Baasonen/Vene2.0/CAD/VENE.SLDASM

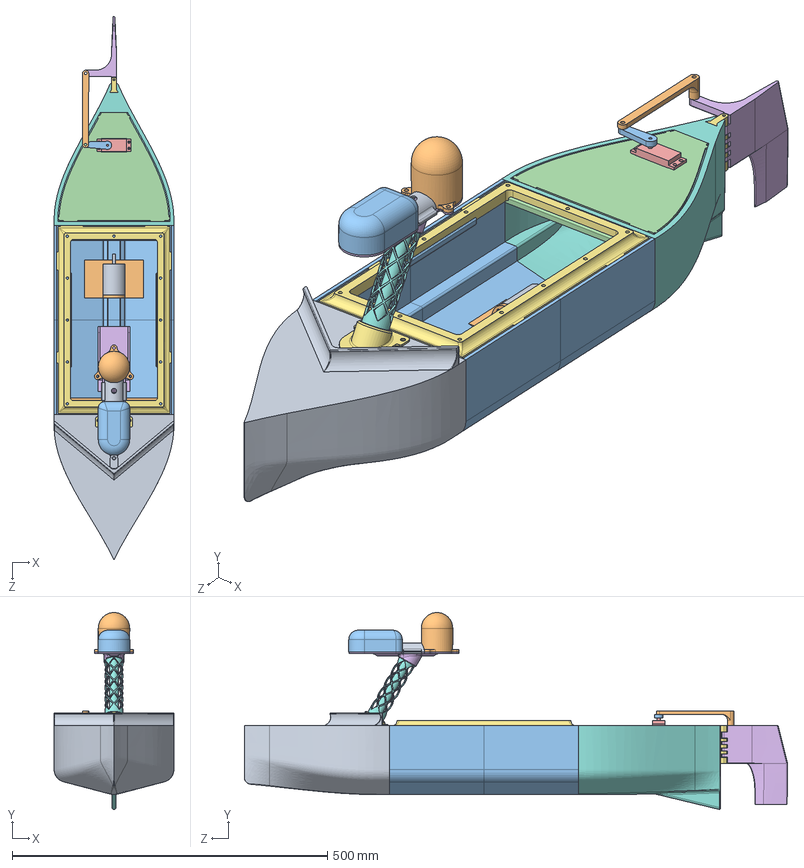
[picture p1: CAD file, 2026-08-04]
CAD/VENE.SLDASM
190.1 x 312.4 x 861.5 mm
HULLMID x 2
MOTORBASE1
MOTORPLACEHOLDER
HULLAFT_2
RUDDERATTACHMENT
RUDDER
SERVO_MG996R
AFT_DECK
SERVO_HORN
RUDDER_LINKAGE
HULLBOW
MAST
MAST_DECK_ATTACHMENT
MAST_END
NEO_6M_BRACKET
NEO_6M_ANTENNA_BRACKET
GPS_SHROUD
LORA_DOME
MAST_END_COVER
PROP_SHAFT_SUPPORT
MAIN_HATCH
BATTER_HOLDER
ESP_HOLDER
HATCH_BRIM_REAR
HATCH_BRIM_SIDE x 2
HATCH_BRIM_FRONT
BOW_PLOW
