Baasonen/Vene2.0/CAD/HULLBOW.SLDPRT

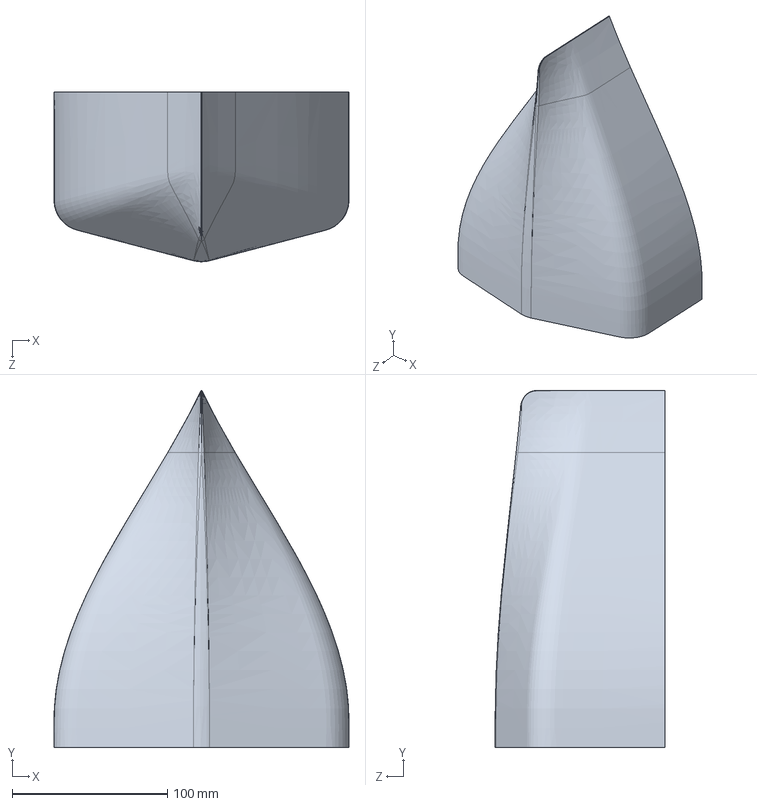
[picture p16: CAD file, 2026-07-09]
CAD/HULLBOW.SLDPRT
190.1 x 230.0 x 109.3 mm
