Baasonen/Vene2.0/CAD/MAST_DECK_ATTACHMENT.SLDPRT

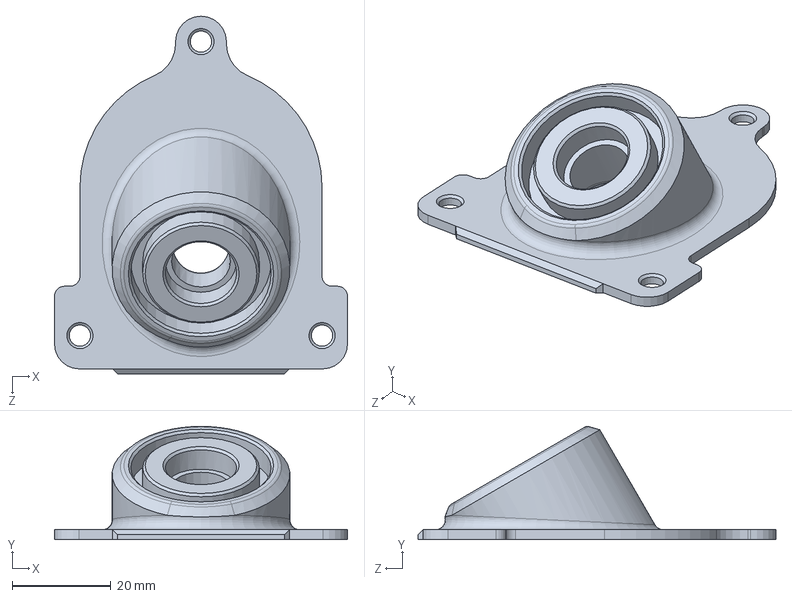
[picture p17: CAD file, 2026-06-03]
CAD/MAST_DECK_ATTACHMENT.SLDPRT
59.3 x 22.9 x 72.4 mm
