Baasonen/Vene2.0/CAD/HULLAFT_2.SLDPRT

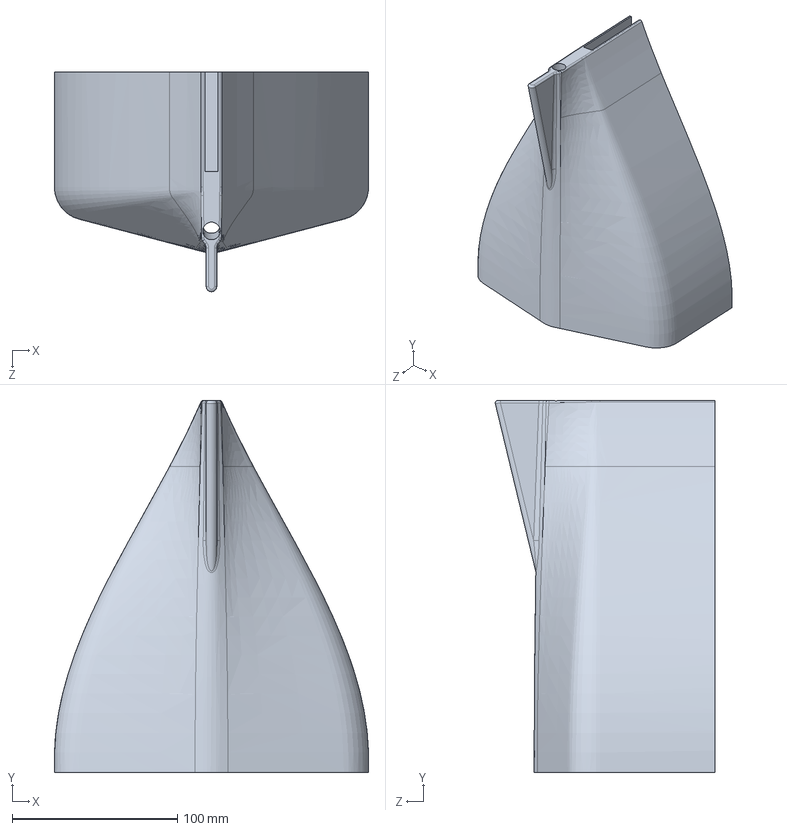
[picture p18: CAD file, 2026-06-03]
CAD/HULLAFT_2.SLDPRT
190.0 x 225.0 x 132.8 mm
