Baasonen/Vene2.0/CAD/PROP_SHAFT_SUPPORT.SLDPRT

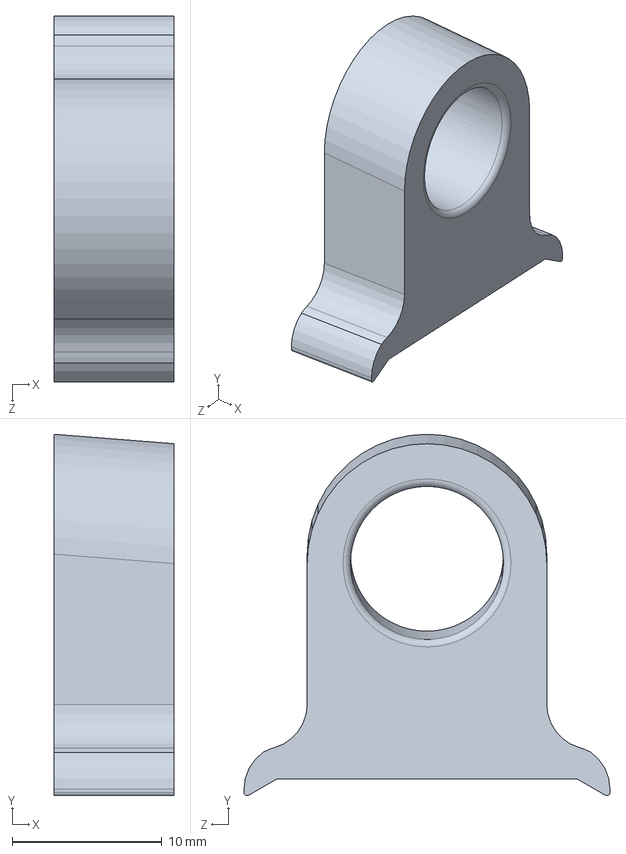
[picture p19: CAD file, 2026-06-03]
CAD/PROP_SHAFT_SUPPORT.SLDPRT
8.00 x 24.1 x 24.4 mm
