Baasonen/Vene2.0/CAD/NEO_6M_ANTENNA_BRACKET.SLDPRT

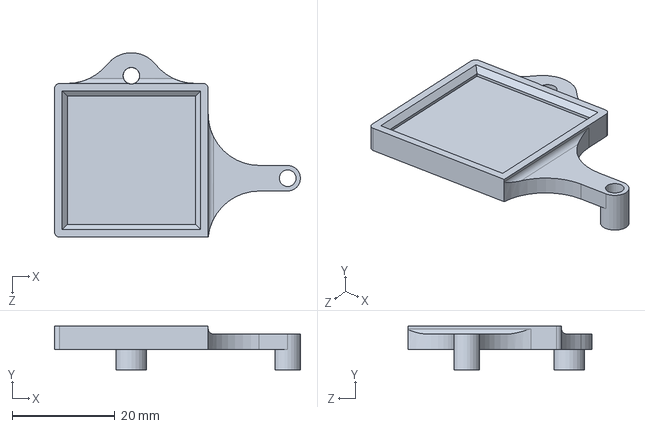
[picture p20: CAD file, 2026-06-03]
CAD/NEO_6M_ANTENNA_BRACKET.SLDPRT
48.0 x 8.50 x 36.0 mm
