Baasonen/Vene2.0/CAD/NEO_6M_BRACKET.SLDPRT

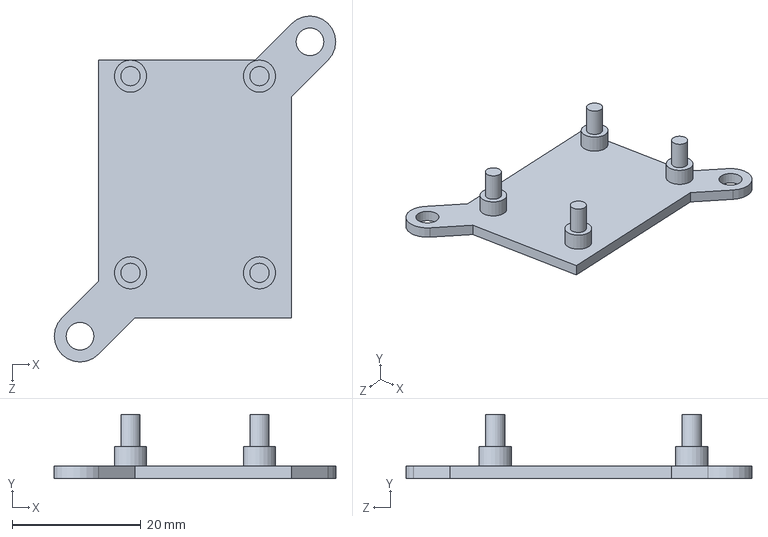
[picture p21: CAD file, 2026-06-03]
CAD/NEO_6M_BRACKET.SLDPRT
43.7 x 10.0 x 53.7 mm
