Baasonen/Vene2.0/CAD/MAST_END.SLDPRT

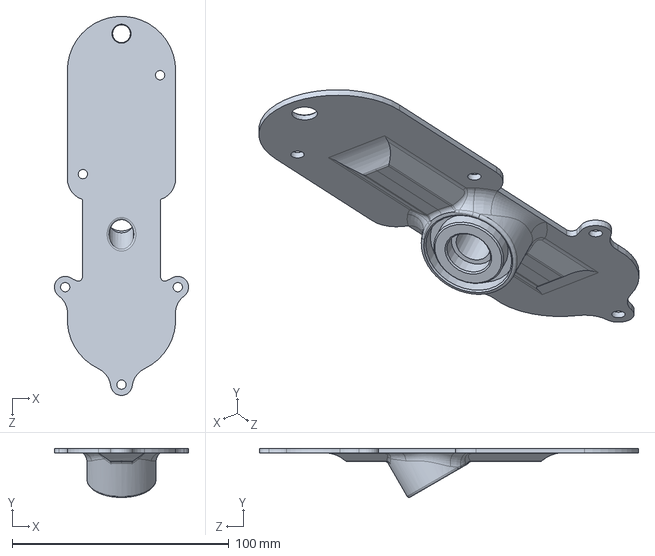
[picture p22: CAD file, 2026-06-03]
CAD/MAST_END.SLDPRT
61.9 x 22.6 x 174.9 mm
