Baasonen/Vene2.0/CAD/MAST_END_COVER.SLDPRT

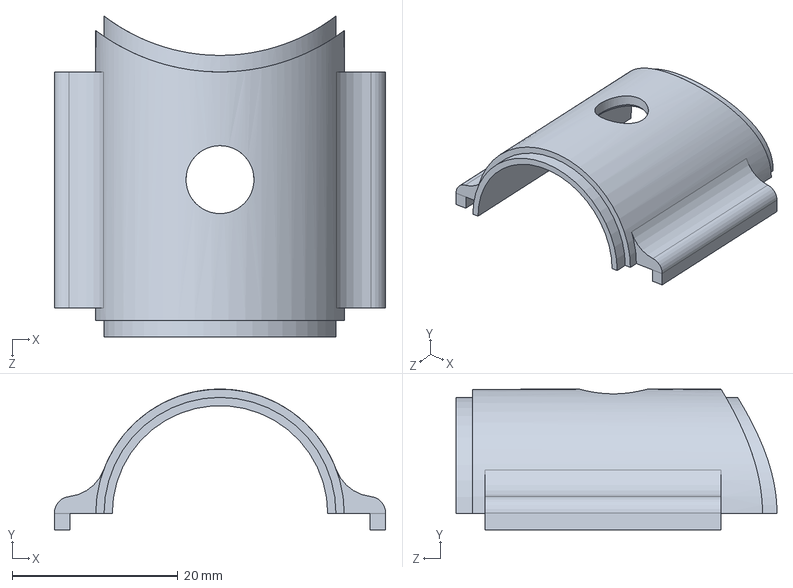
[picture p23: CAD file, 2026-06-03]
CAD/MAST_END_COVER.SLDPRT
40.0 x 17.0 x 38.8 mm
