Baasonen/Vene2.0/CAD/MOTORBASE1.SLDPRT

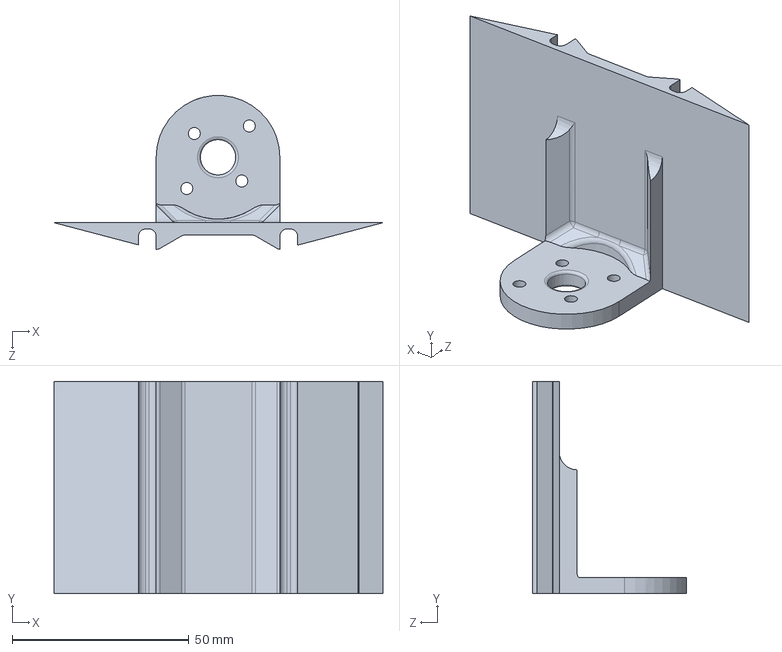
[picture p24: CAD file, 2026-05-25]
CAD/MOTORBASE1.SLDPRT
93.1 x 60.0 x 43.5 mm
