Baasonen/Vene2.0/CAD/RUDDER.SLDPRT

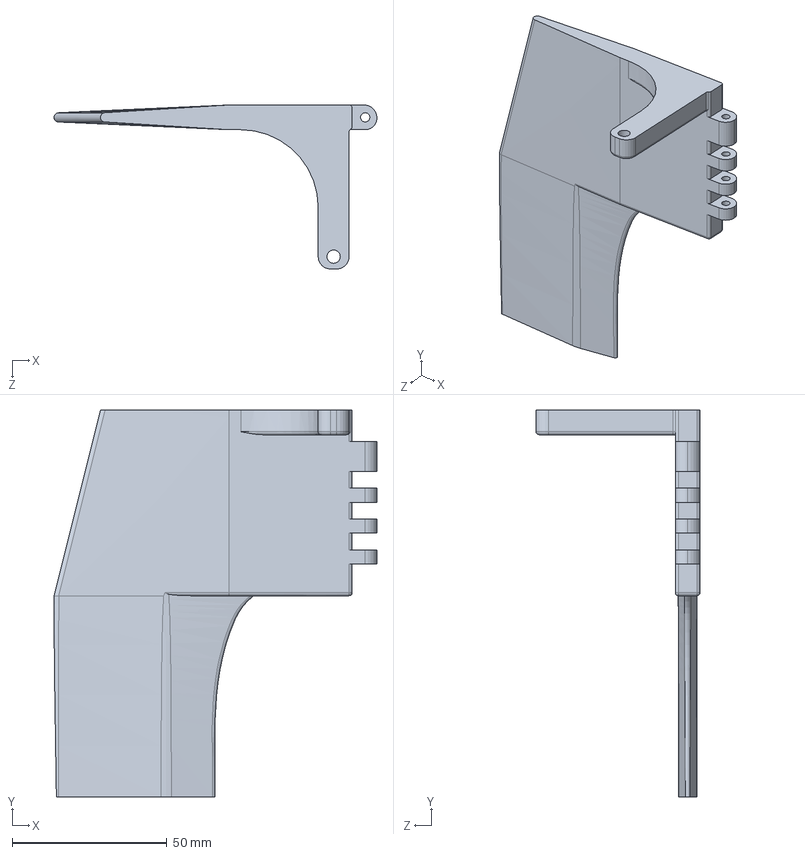
[picture p25: CAD file, 2026-05-25]
CAD/RUDDER.SLDPRT
104.3 x 125.0 x 53.0 mm
