Baasonen/Vene2.0/CAD/RUDDERATTACHMENT.SLDPRT

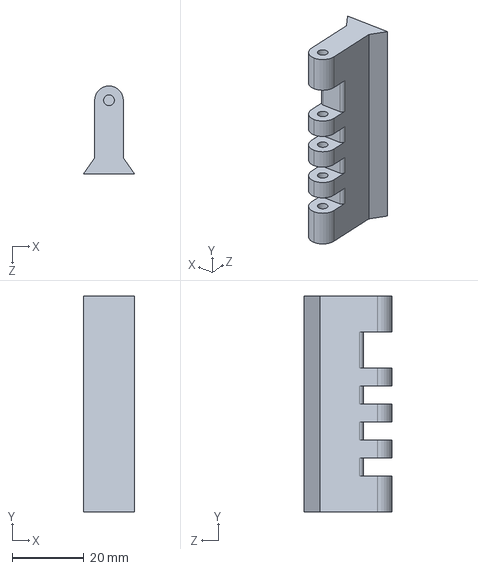
[picture p26: CAD file, 2026-05-25]
CAD/RUDDERATTACHMENT.SLDPRT
14.3 x 60.0 x 24.5 mm
