Baasonen/Vene2.0/CAD/AFT_DECK_GUIDE.SLDPRT

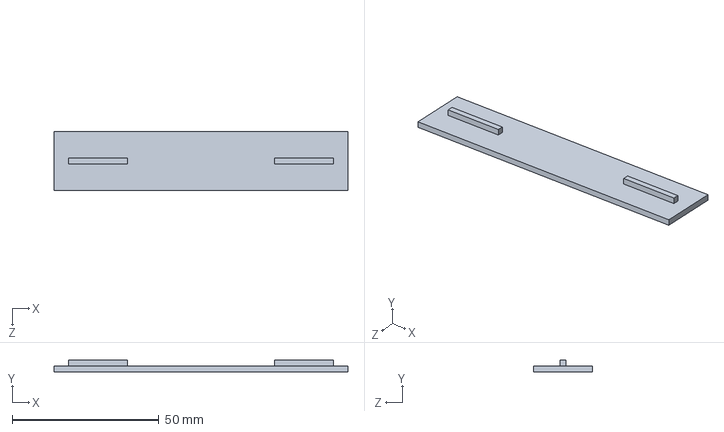
[picture p27: CAD file, 2026-05-25]
CAD/AFT_DECK_GUIDE.SLDPRT
100.0 x 4.00 x 20.0 mm
