Baasonen/Vene2.0/CAD/MAST.SLDPRT

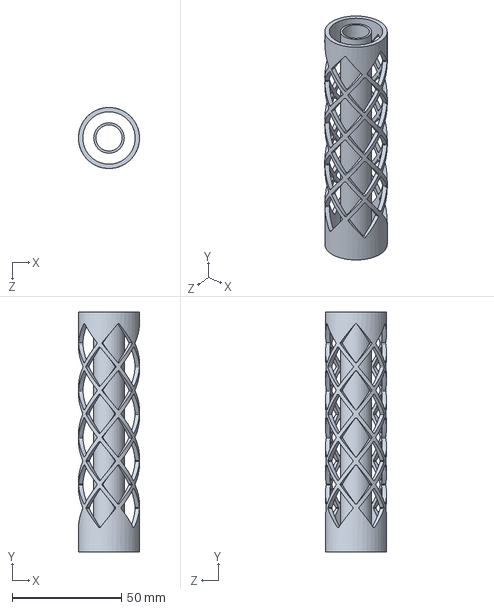
[picture p28: CAD file, 2026-05-25]
CAD/MAST.SLDPRT
28.0 x 110.0 x 28.0 mm
