Baasonen/Vene2.0/CAD/SERVO_HORN.SLDPRT

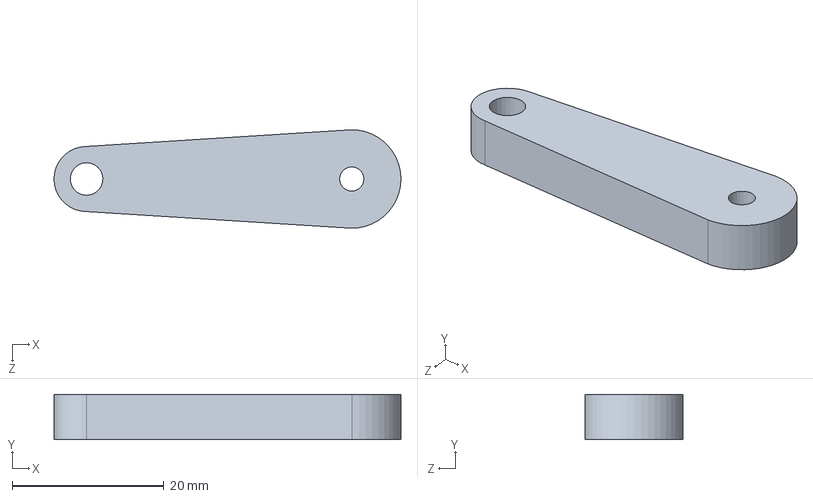
[picture p29: CAD file, 2026-05-25]
CAD/SERVO_HORN.SLDPRT
45.8 x 6.00 x 13.0 mm
