Baasonen/Vene2.0/CAD/HULLMID.SLDPRT

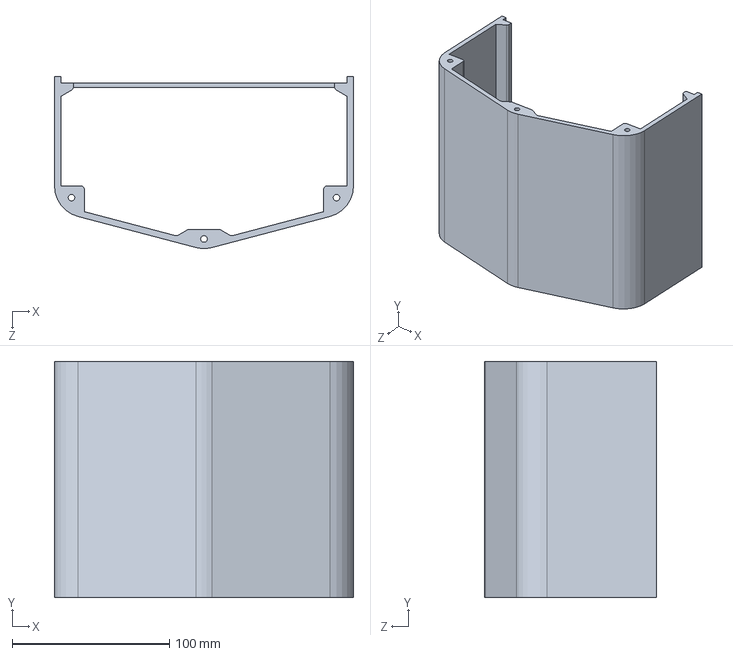
[picture p30: CAD file, 2026-05-25]
CAD/HULLMID.SLDPRT
190.0 x 150.0 x 109.2 mm
