Baasonen/Vene2.0/CAD/SERVO_MG996R.SLDPRT

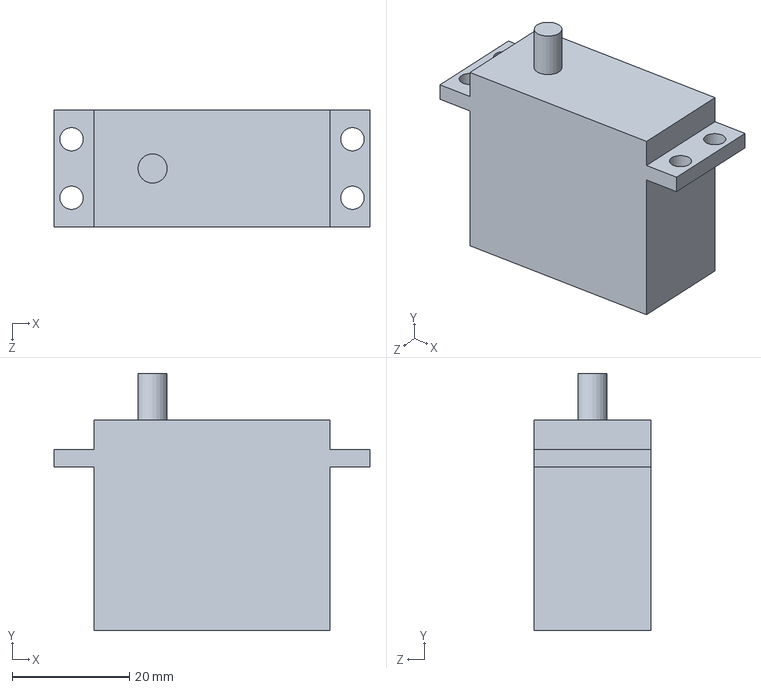
[picture p31: CAD file, 2026-05-25]
CAD/SERVO_MG996R.SLDPRT
54.0 x 44.0 x 20.0 mm
