Baasonen/Vene2.0/CAD/RUDDER_LINKAGE.SLDPRT

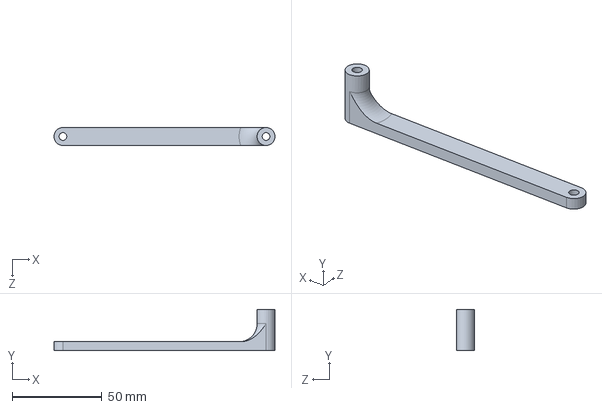
[picture p32: CAD file, 2026-05-25]
CAD/RUDDER_LINKAGE.SLDPRT
122.9 x 23.0 x 10.0 mm
