Baasonen/Vene2.0/CAD/LORA_DOME.SLDPRT

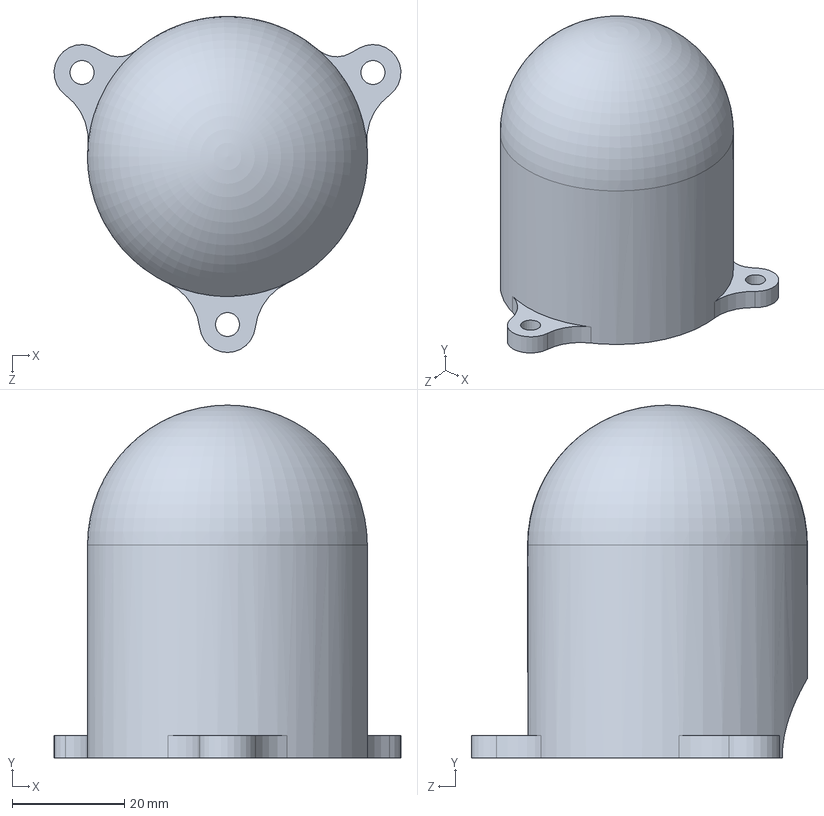
[picture p33: CAD file, 2026-05-25]
CAD/LORA_DOME.SLDPRT
61.9 x 63.0 x 60.0 mm
