Baasonen/Vene2.0/CAD/GPS_SHROUD.SLDPRT

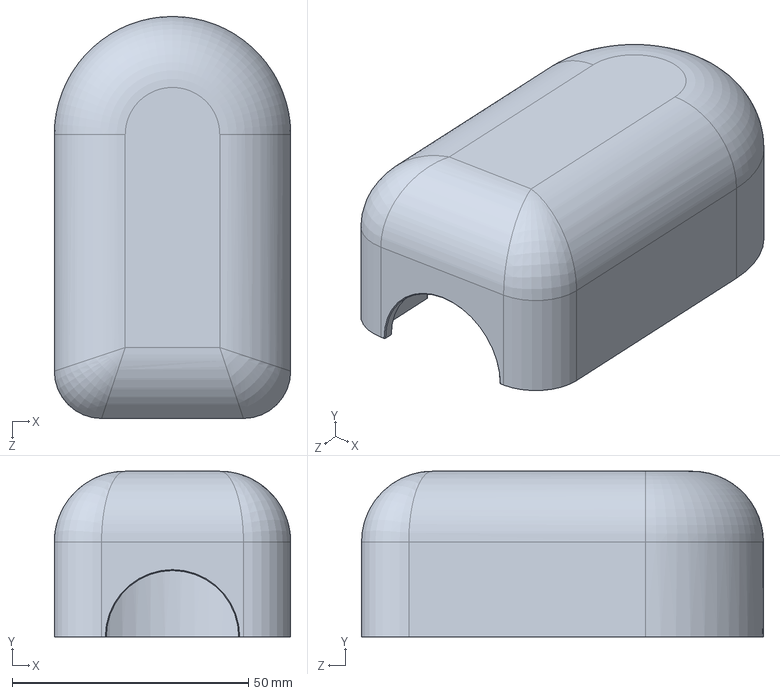
[picture p34: CAD file, 2026-05-25]
CAD/GPS_SHROUD.SLDPRT
50.0 x 35.0 x 85.0 mm
