Baasonen/Vene2.0/CAD/MOTORMOUNT_GUIDE.SLDPRT

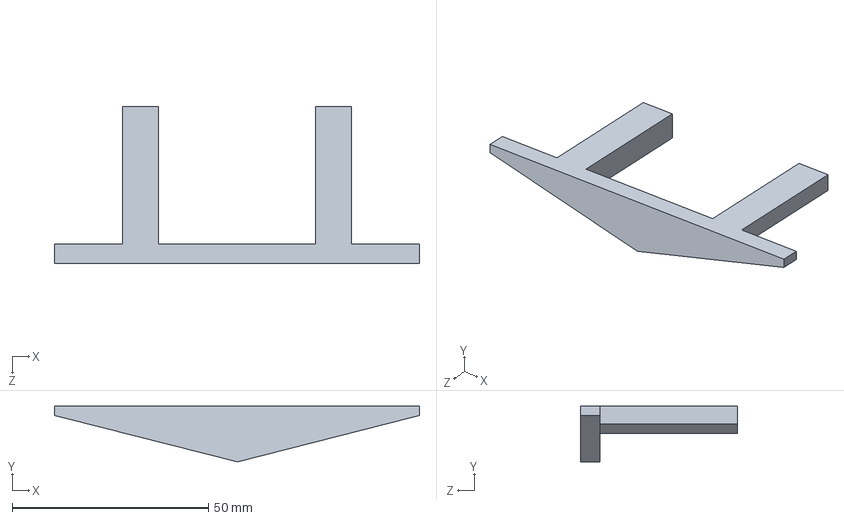
[picture p35: CAD file, 2026-05-17]
CAD/MOTORMOUNT_GUIDE.SLDPRT
93.1 x 14.2 x 40.0 mm
