Baasonen/Vene2.0/CAD/MOTORPLACEHOLDER.SLDPRT

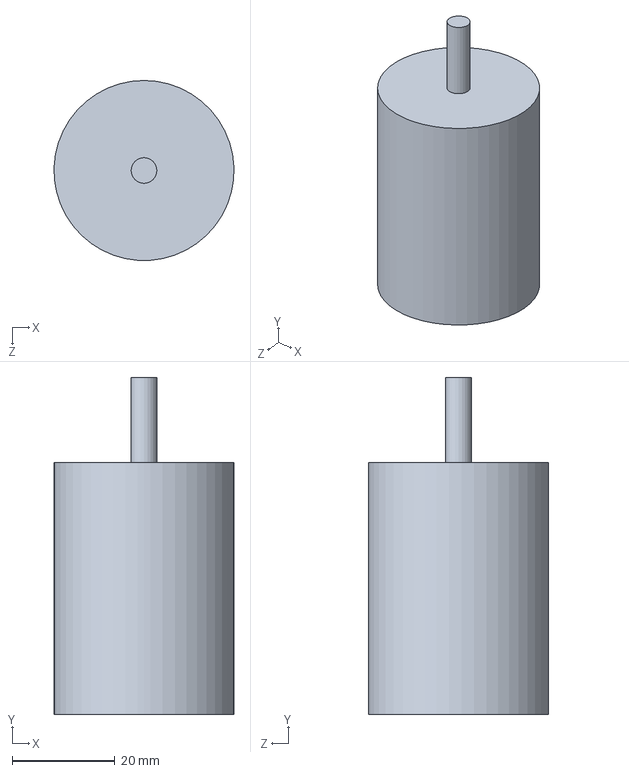
[picture p36: CAD file, 2026-05-17]
CAD/MOTORPLACEHOLDER.SLDPRT
35.0 x 65.5 x 35.0 mm
