Baasonen/Vene2.0/CAD/PROP_COLLIDER.SLDPRT

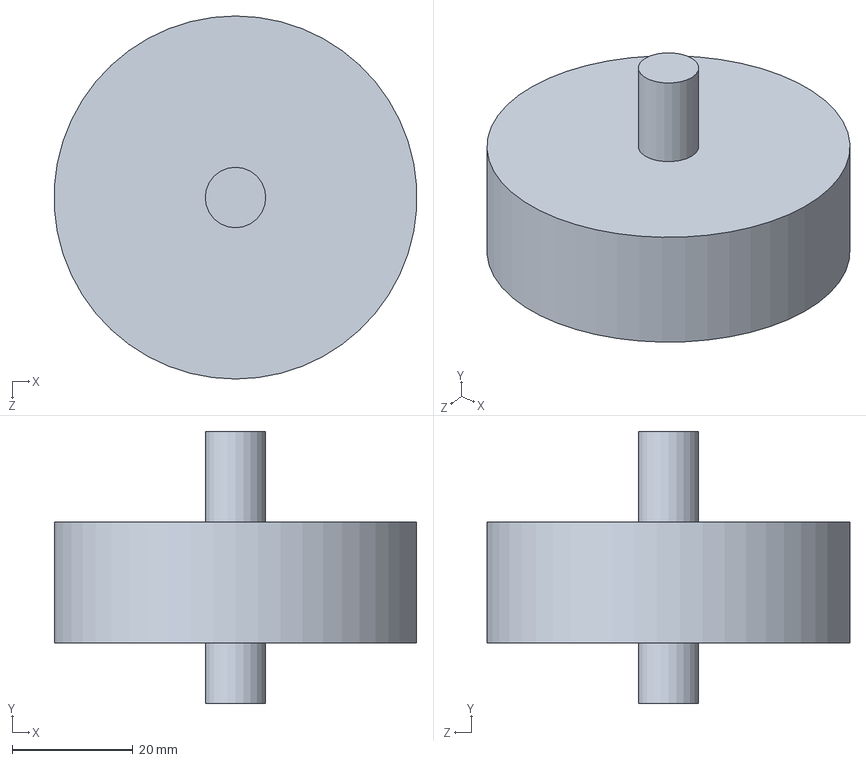
[picture p37: CAD file, 2026-05-17]
CAD/PROP_COLLIDER.SLDPRT
59.9 x 45.0 x 60.0 mm
