Baasonen/Vene2.0/CAD/Proto.SLDPRT

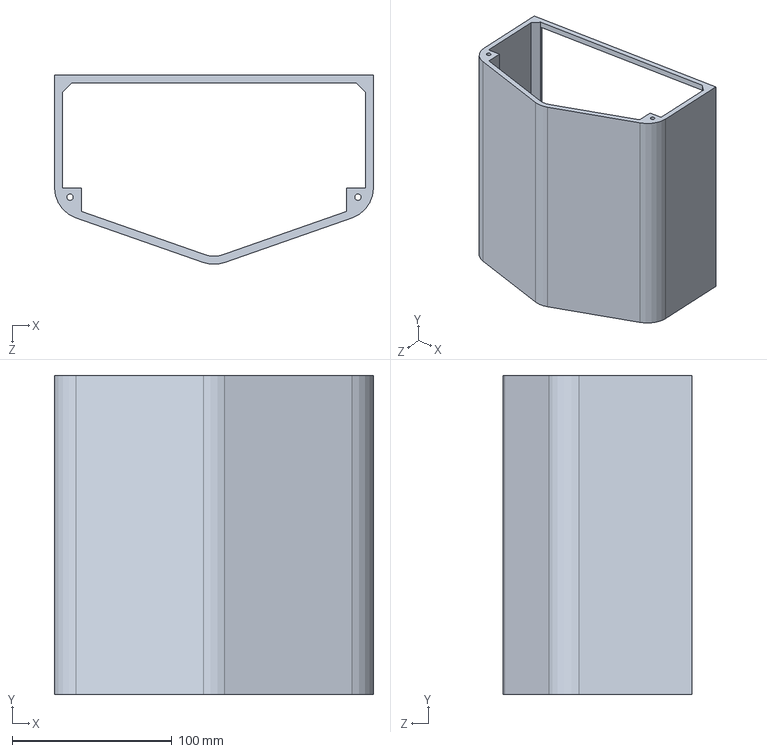
[picture p38: CAD file, 2026-05-06]
CAD/Proto.SLDPRT
200.0 x 200.0 x 118.7 mm
