Baasonen/Vene2.0/CAD/Body1.SLDPRT

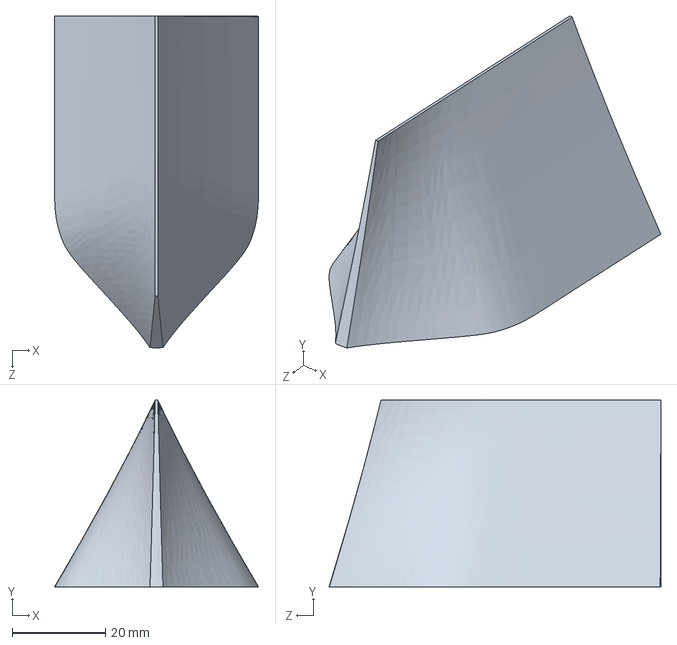
[picture p39: CAD file, 2026-05-06]
CAD/Body1.SLDPRT
43.7 x 40.0 x 71.1 mm
