Baasonen/Vene2.0/CAD/Body2.SLDPRT

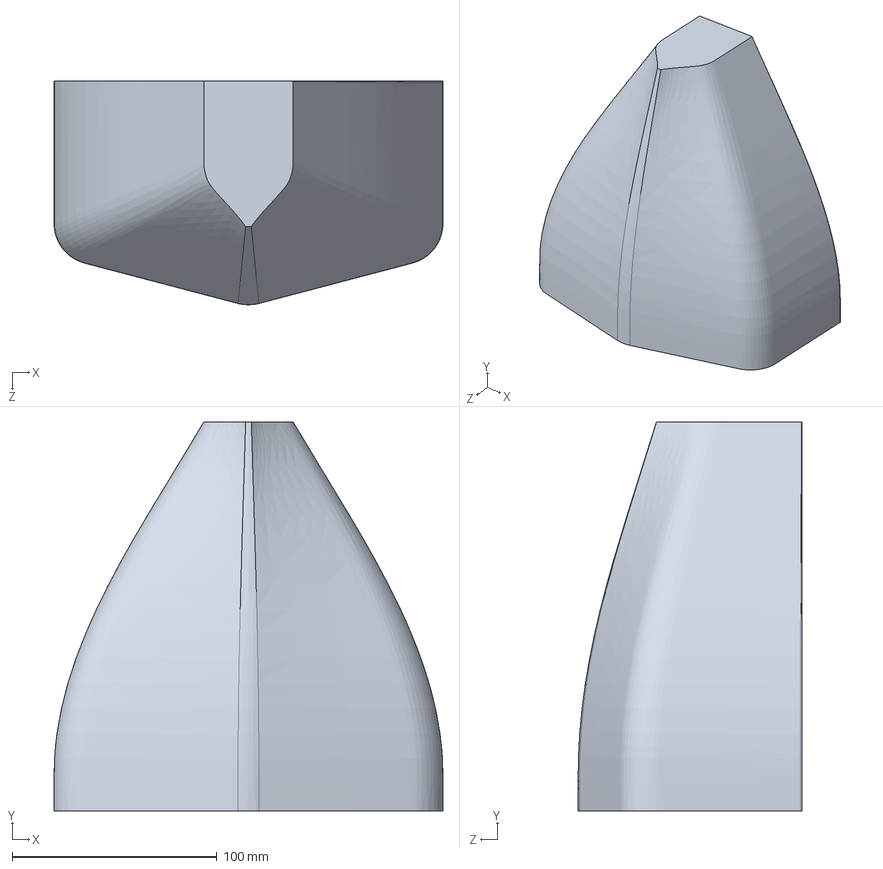
[picture p40: CAD file, 2026-05-06]
CAD/Body2.SLDPRT
190.1 x 190.0 x 109.3 mm
