Baasonen/Vene2.0/ESP/include/state.h

#pragma once

#include "gps.h"
#include "magnetometer.h"
#include "LKF.h"
#include "battery.h"
#include "tuning.h"

struct wp
{
    double lat, lon;
};

typedef struct 
{   
    wp waypoints[WP_AMMOUNT_LIM + 1];
    uint8_t id;
    uint8_t length;
    bool newRouteAvailable;
} Route;

typedef struct 
{
    uint8_t mode;
    uint8_t targetWaypoint;
    int16_t targetCourse;
    int8_t APThrottle;

    bool loraTimeout;
    int8_t loraRSSI;
    bool wifiTimeout;
    uint32_t loraTimeoutTriggerTime;

    wp home;
    bool homeSet;
    bool homeNeedsSave;
    bool ctrlArmed;

    bool routeReady;

    uint32_t errorCode;
    uint32_t unixTime;
    bool timeSet;
} SystemStatus;

typedef struct 
{
    int8_t throttle;
    int8_t rudder;
} ManualControls;

typedef struct 
{
    GPSData gps;
    MagData mag;
    PosSol kf;
} SensorData;

typedef struct 
{
    SensorData sensors;
    Route route;
    SystemStatus status;
    Battery battery;
    ManualControls manual;
} State;

extern State globalState;
extern SemaphoreHandle_t stateMutex;
extern QueueHandle_t sensorQueue;

uint8_t validateMode(const SystemStatus& status, const SensorData& sensors);
