Baasonen/Vene2.0/ESP/src/errors.cpp

#include "errors.h"

#define ERROR_TASK_PERIOD_MS 200
#define WI_SAMPLE_PERIOD_MS 2000
#define WI_SAMPLE_DIVIDER (WI_SAMPLE_PERIOD_MS / ERROR_TASK_PERIOD_MS)
#define DEBOUNCE_THRESHOLD 5
#define GPS_DEBOUNCE_THRESHOLD 30

struct Debounce
{
    uint8_t counter = 0;
};

static uint32_t readWaterIngressSensor()
{
    digitalWrite(WI_SENSOR_VCC, HIGH);
    delayMicroseconds(WI_SETTLE_US); // Wait to settle
    uint32_t reading = analogRead(WI_SENSOR_S);
    digitalWrite(WI_SENSOR_VCC, LOW);
    return reading;
}

static bool debounce(Debounce& d, bool condition, uint8_t treshold = DEBOUNCE_THRESHOLD)
{
    if (condition)
    {
        if (d.counter < treshold) {d.counter++;}
    }
    else
    {
        if (d.counter > 0) {d.counter--;}
    }
    return d.counter >= treshold;
}

void errorTask(void* pv)
{
    esp_task_wdt_add(NULL);

    pinMode(WI_SENSOR_VCC, OUTPUT);
    digitalWrite(WI_SENSOR_VCC, LOW);
    pinMode(WI_SENSOR_S, INPUT);

    static Debounce gpsFailDb, gpsAccDb, magFailDb, magAccDb, battDb;
    static uint32_t loopCounter = 0;
    static uint32_t waterLevel = false;

    TickType_t xLastWakeTime = xTaskGetTickCount();
    const TickType_t xPeriod = pdMS_TO_TICKS(ERROR_TASK_PERIOD_MS);

    for (;;)
    {
        vTaskDelayUntil(&xLastWakeTime, xPeriod);
        esp_task_wdt_reset();

        SensorData sensors = {};
        SystemStatus status = {};
        Battery battery = {};
        Route route = {};

        xQueuePeek(sensorQueue, &sensors, 0);

        if (xSemaphoreTake(stateMutex, pdMS_TO_TICKS(10)) == pdTRUE)
        {
            status = globalState.status;
            battery = globalState.battery;
            route = globalState.route;
            xSemaphoreGive(stateMutex);
        }

        if (loopCounter % WI_SAMPLE_DIVIDER == 0)
        {
            waterLevel = readWaterIngressSensor();
            //Serial.println(waterLevel);
        }
        loopCounter++;

        setErrorIf(ERR_GPS_FAIL, debounce(gpsFailDb, !sensors.gps.valid));
        setErrorIf(ERR_MAG_FAIL, debounce(magFailDb, !sensors.mag.valid));
        setErrorIf(ERR_GPS_ACC_LOW, debounce(gpsAccDb, !sensors.kf.accurate, GPS_DEBOUNCE_THRESHOLD));
        setErrorIf(ERR_MAG_ACC_LOW, debounce(magAccDb, sensors.mag.accuracy < MAG_MIN_ACC));
        setErrorIf(ERR_BATT_LOW, debounce(battDb, battery.lowest < BATT_LOW_TRESHOLD));
        setErrorIf(ERR_KF_UNINIT, !sensors.kf.valid);

        setErrorIf(ERR_LORA_TIMEOUT, status.loraTimeout);
        setErrorIf(ERR_WIFI_TIMEOUT, status.wifiTimeout);

        setErrorIf(ERR_NO_ROUTE, !status.routeReady);
        setErrorIf(ERR_NO_HOME, !status.homeSet);

        if (waterLevel > 200) {setError(ERR_WATER_LOW);}
        if (waterLevel > 450) {setError(ERR_WATER_MID);}
        if (waterLevel > 1500) {setError(ERR_WATER_HIGH);}

        clearError(ERR_HDG_A1);        
        clearError(ERR_HDG_A2);
        clearError(ERR_HDG_A3);
        switch(sensors.mag.accuracy)
        {
            case 1: setError(ERR_HDG_A1); break;
            case 2: setError(ERR_HDG_A2); break;
            case 3: setError(ERR_HDG_A3); break;
            default: break;
        }
    }
}
