Baasonen/Vene2.0/ESP/include/lora.h

#pragma once

#include <RadioLib.h>
#include <SPI.h>

#include "esp_system.h"
#include "esp_task_wdt.h"

#include "state.h"
#include "tuning.h"

#define LORA_SCK 14
#define LORA_MISO 26
#define LORA_MOSI 13
#define LORA_CS 15
#define LORA_DIO0 12
#define LORA_RST 25

#define LORA_FREQ 869.5
#define LORA_BANDWIDTH 125.0
#define LORA_SF 9
#define LORA_CODING_RATE 5
#define LORA_POWER 20

#define LORA_TX_TIMEOUT_MS 750

#define PKT_WP_DATA 0x01
#define PKT_TELE_FAST 0x02
#define PKT_TELE_SLOW 0x03
#define PKT_BE_TELE 0x13
#define PKT_CONTROL 0x04
#define PKT_RESET_ERRORS 0x07
#define PKT_DATA 0x10

#define PKT_HOME_SET 0x08
#define PKT_HOME_DATA 0x09
#define PKT_HOME_REQ 0x0A
#define PKT_TIME_REQ 0x0B
#define PKT_TIME_DATA 0x0C
#define PKT_COURSE_SET 0x0D
#define PKT_COURSE_DATA 0x0E
#define PKT_UPLOAD_BEGIN 0x0F
#define PKT_THR_SET 0x11
#define PKT_THR_DATA 0x12

#pragma pack(push, 1)

struct TelemetryFastPacket
{
    uint8_t packetID; // 0x02
    uint16_t heading;
    uint8_t mode;
    uint8_t targetIdx; 
};

struct TelemetrySlowPacket
{
    uint8_t packetID; // 0x03
    uint8_t gps;
    uint8_t signalStrength;
    int32_t lat;
    int32_t lon;
};

struct BeTelemetryPacket
{   
    uint8_t packetID;
    uint8_t c1;
    uint8_t c2;
    uint8_t c3;
    uint32_t errorCode;
};

struct RoutePacket
{
    uint8_t packetID; // 0x01
    uint8_t id;
    double lat;
    double lon;
    uint8_t order;
    uint8_t ammnt;
};

struct ResetErrorsPacket
{
    uint8_t packetID; // 0x07
};

struct DataPacket
{
    uint8_t packetID; // 0x10
    uint8_t id;
    uint8_t data;
};

struct ControlPacket
{
    uint8_t packetID;
    uint8_t mode;
};

struct HomeSetPacket // From GUI: Set homeWP
{
    uint8_t packedID; // 0x08
    double lat;
    double lon;
};

struct HomeDataPacket // Respond to PKT_HOME_REQ from GUI
{
    uint8_t packetID; // 0x09
    double lat;
    double lon;
};

struct TimeDataPacket
{
    uint8_t packetID; // 0x0C
    uint32_t unixTime;
};

struct CourseSetPacket
{
    uint8_t packetID;
    int16_t course;
};

struct CourseDataPacket
{
    uint8_t packetID;
    int16_t course;
};

struct ThrottlePacket
{
    uint8_t packetID;
    int8_t throttle;
};

#pragma pack(pop)

extern SemaphoreHandle_t stateMutex;

int LoRaInit();

void commsTask(void* pvParameters);

void beginTransmit(uint8_t* data, size_t len);
