Baasonen/Vene2.0/VGUI2/vcom/protocol.py

import os
import struct

from enum import Enum, auto
from typing import Dict, Tuple

# Struct formats

# Fast telemetry (downlink): position, heading, mode, target waypoint
FAST_FORMAT = "<BHBB"
FAST_SIZE = struct.calcsize(FAST_FORMAT)
 
# Slow telemetry (downlink): battery, HDOP, RSSI, error bitmask
SLOW_FORMAT = "<BBBii"
SLOW_SIZE = struct.calcsize(SLOW_FORMAT)

# BE telemetry (downlink): uint8_t packetID, uint8_t c1, uint8_t c2, uint8_t c3, uint32_t errorCode
BE_TELE_FORMAT = "<BBBBI"
BE_TELE_SIZE = struct.calcsize(BE_TELE_FORMAT)
 
# Waypoint data (uplink): route_id, lat, lon, waypoint order, total count
ROUTE_FORMAT = "<BBddBB"
 
# General-purpose ACK / heartbeat (bidirectional)
ACK_FORMAT = "<BBB"
ACK_SIZE = struct.calcsize(ACK_FORMAT)
 
# Mode change command (uplink)
CONTROL_FORMAT = "<BB"
 
# Manual throttle / rudder (uplink, 10 Hz)
MANUAL_FORMAT = "<Bbb"
 
# Error-flag reset command (uplink, single byte)
RESET_ERRORS_FORMAT = "<B"
 
# WiFi heartbeat from boat (downlink)
WIFI_HEARTBEAT_FORMAT = "<BI"
WIFI_HEARTBEAT_SIZE = struct.calcsize(WIFI_HEARTBEAT_FORMAT)
 
# Home waypoint: used for PKT_HOME_SET (uplink) and PKT_HOME_DATA (downlink)
HOME_FORMAT = "<Bdd"
HOME_SIZE = struct.calcsize(HOME_FORMAT)
 
# Unix-time response (uplink)
TIME_DATA_FORMAT = "<BI"
TIME_DATA_SIZE = struct.calcsize(TIME_DATA_FORMAT)

COURSE_SET_FORMAT = "<Bh"
COURSE_SET_SIZE = struct.calcsize(COURSE_SET_FORMAT)

COURSE_DATA_FORMAT = "<Bh"
COURSE_DATA_SIZE = struct.calcsize(COURSE_DATA_FORMAT)

THR_SET_FORMAT = "<Bb"
THR_SET_SIZE = struct.calcsize(THR_SET_FORMAT)

THR_DATA_FORMAT = "<Bb"
THR_DATA_SIZE = struct.calcsize(THR_DATA_FORMAT)


# Packet IDs

PKT_WP_DATA = 0x01 # U : WP data during upload
PKT_TELE_FAST = 0x02 # D : High-rate tele
PKT_TELE_SLOW = 0x03 # D : Low-rate tele
PKT_CONTROL = 0x04 # U : Mode change command
PKT_MANUAL = 0x05 # U : Manual steering commands
PKT_WIFI_HB = 0x06 # D : WiFi hb 
PKT_RESET_ERRORS = 0x07 # U : Clear error data 
PKT_HOME_SET = 0x08 # U : Send new home wp
PKT_HOME_DATA = 0x09 # D : Current home wp
PKT_HOME_REQ = 0x0A # U : Request current home wp 
PKT_TIME_REQ = 0x0B # D : Requests unix time
PKT_TIME_DATA = 0x0C # U : Send unix time
PKT_DATA = 0x10 # U/D : ACK payload / hb
PKT_COURSE_SET = 0x0D # U : Set or request (-1) target course
PKT_COURSE_DATA = 0x0E # D : Currently set target course (for MODE_CRS)
PKT_THR_SET = 0x11 # U : Set or request (-110) A/P throttle
PKT_THR_DATA = 0x12 # D : Currently set A/P throttle
PKT_BE_TELE = 0x13 # D : Battery cell voltages & error code
PKT_UPLOAD_BEGIN = 0x0F

# Modes

MODE_STOP = 0
MODE_MANUAL = 1
MODE_AUTO = 2
MODE_RTH = 3
MODE_COURSE = 4

MODE_NAMES: Dict[int, str] ={
    MODE_STOP : "STOP",
    MODE_MANUAL : "MANUAL",
    MODE_AUTO : "A/P",
    MODE_RTH : "RTH",
    MODE_COURSE : "CRS"
}

# Retry / timeout limits

MODE_TIMEOUT_S = 3.5 # Seconds to wait for mode-change ACK
MODE_RETRIES = 5

ROUTE_TIMEOUT_S = 2.0 # Seconds to wait for each wp ACK
ROUTE_RETRIES = 5

HOME_TIMEOUT_S = 4.2 # Seconds to wait for a home set or home data ACK
HOME_RETRIES = 5

LORA_STALE_S = 10.0 # Time limit for LoRa timeout
WIFI_STALE_S = 2.0 # Time limit for WiFi timeout

COURSE_SCALE = 1 # 1 for whole deg res, 10 for 1/10 deg resolution
COURSE_REQ = -1

COURSE_TIMEOUT_S = 1.8
COURSE_RETRIES = 10

THR_REQ = -110

THR_TIMEOUT_S = 1.7
THR_RETRIES = 10

# Upload state

class uploadStatus(Enum):
    IDLE = auto()
    UPLOADING = auto()
    DONE = auto()
    FAILED = auto()

# Error bit definitions

_DEFAULT_ERROR_BITS : Dict[int, Tuple[str, str]] = {
    0: ("ERR_DEF", "Could not load error definitions from file"),
}

_DEFAULT_ERR_PATH = os.path.join(os.path.dirname(__file__), "error_codes.txt")

def load_error_defs(path: str = _DEFAULT_ERR_PATH) -> Dict[int, Tuple[str, str]]:
    defs: Dict[int, Tuple[str, str]] = dict(_DEFAULT_ERROR_BITS)

    if not os.path.isfile(path):
        print("error_codes.txt not found")
        return defs
    
    with open(path, encoding = "utf-8") as f:
        for raw in f:
            line = raw.strip()
            if not line or line.startswith("#") or "=" not in line:
                continue

            bit_str, rest = line.split("=", 1)
            bit_str = bit_str.strip().upper()

            if not bit_str.startswith("BIT"):
                continue
            
            try:
                bit_num = int(bit_str[3:])
            
            except ValueError:
                continue

            name, desc = rest.split(":", 1) if ":" in rest else (rest, "")
            defs[bit_num] = (name.strip(), desc.strip())

    return defs
