Baasonen/Vene2.0/ESP/include/magnetometer.h

#pragma once

#include <Adafruit_BNO08x.h>
#include <Arduino.h>


#define SH2_ROTATION_VECTOR 0x05

typedef struct 
{
    float heading;
    unsigned char accuracy;
    bool valid;
} MagData;

int magInit();
MagData getMagnetometer();
